2ME3Elektronika/25-26_Snack-o-Matic/Impresiones 3D/Soporte motor/Soporte Motor Completo.jpg

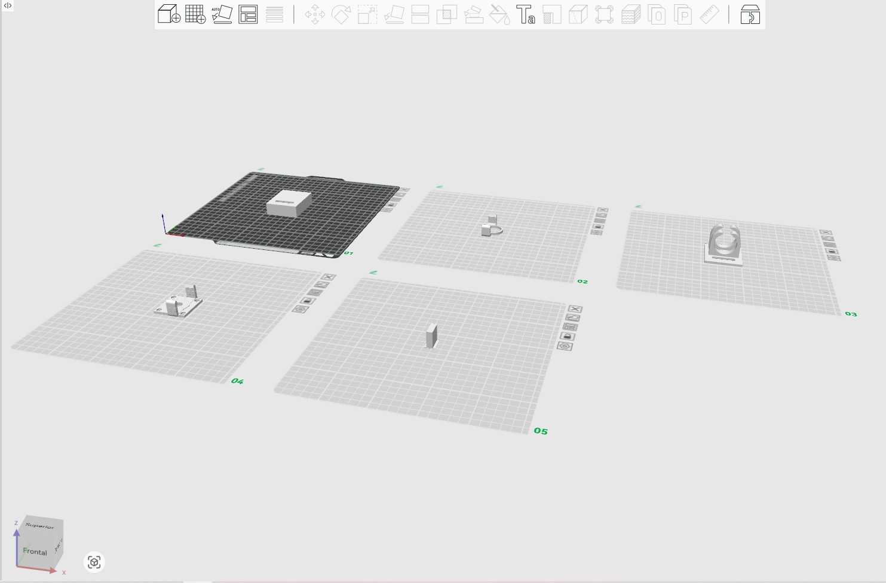
Impresiones 3D/Soporte motor/Soporte Motor Completo.jpg
