2ME3Elektronika/25-26_Snack-o-Matic/Prototipos/Prototipo foto 1.jpeg

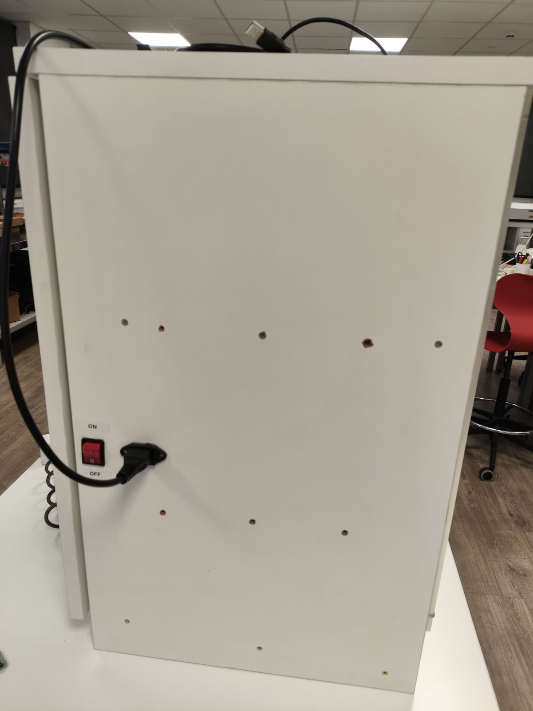
Prototipos/Prototipo foto 1.jpeg
