2ME3Elektronika/25-26_Snack-o-Matic/Impresiones 3D/Divisor de monedas/Modelos sin modificar/sorter-customizer_basebox20150919-17856-1al7uiw-0.stl

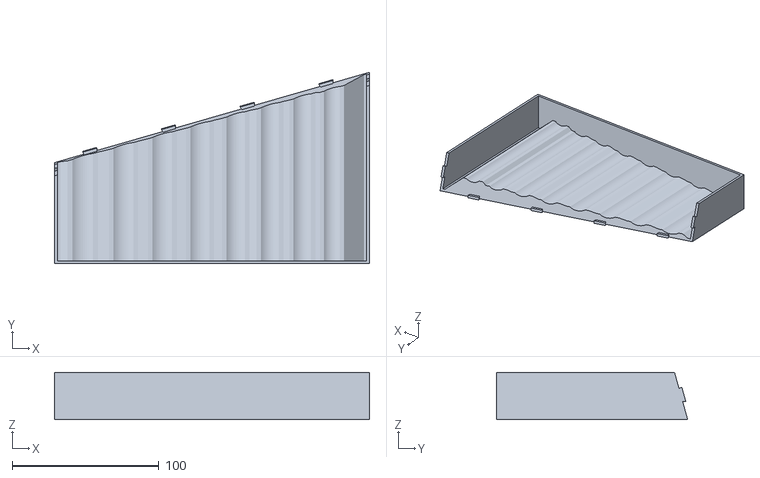
[picture p23: CAD file, 2026-01-08]
Impresiones 3D/Divisor de monedas/Modelos sin modificar/sorter-customizer_basebox20150919-17856-1al7uiw-0.stl
214.9 x 130.6 x 32.2
