2ME3Elektronika/25-26_Snack-o-Matic/Impresiones 3D/Modulos/Modulos 003.stl

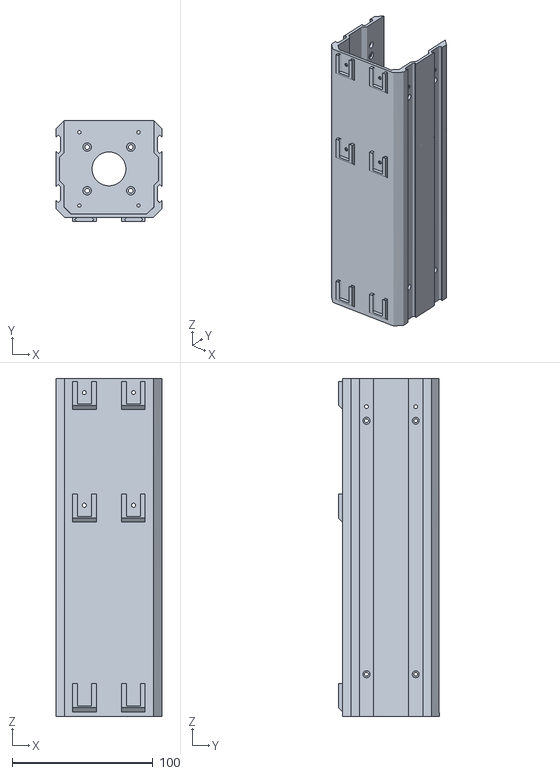
[picture p24: CAD file, 2026-06-03]
Impresiones 3D/Modulos/Modulos 003.stl
75.0 x 72.0 x 240.0
