2ME3Elektronika/25-26_Snack-o-Matic/Impresiones 3D/Monedero/Recoge monedas 4.3mf

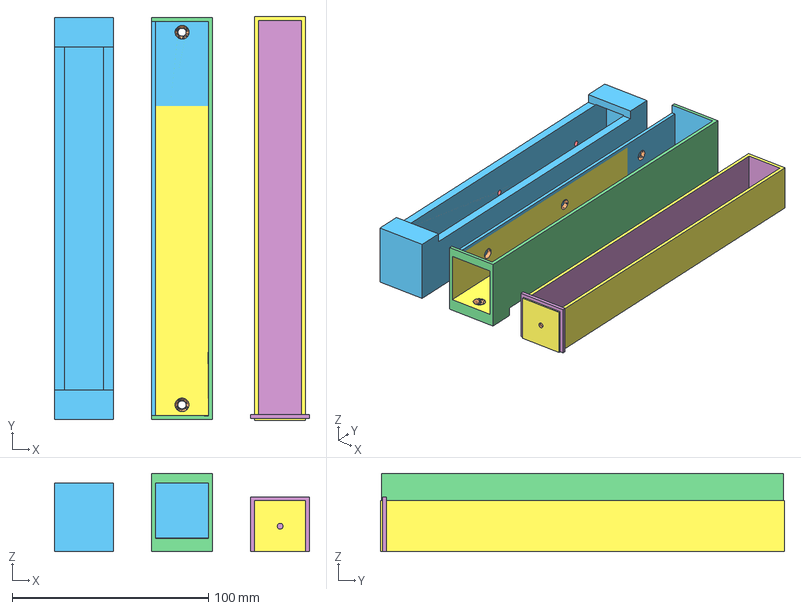
[picture p25: CAD file, 2026-06-03]
Impresiones 3D/Monedero/Recoge monedas 4.3mf
130.0 x 206.0 x 40.0 mm
