2ME3Elektronika/25-26_Snack-o-Matic/Impresiones 3D/Soporte motor/Soporte part 1.3mf

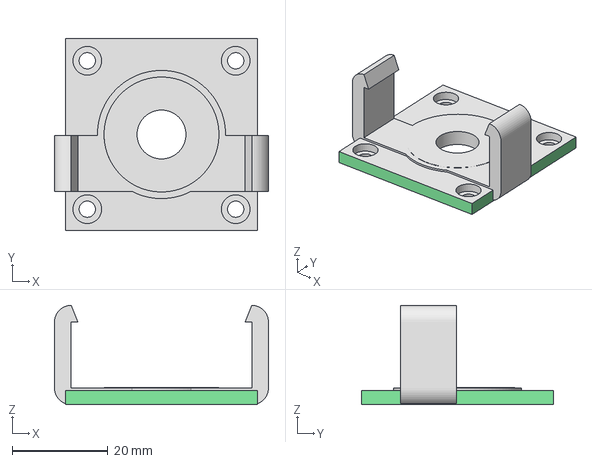
[picture p26: CAD file, 2026-06-03]
Impresiones 3D/Soporte motor/Soporte part 1.3mf
44.7 x 40.0 x 20.8 mm
