2ME3Elektronika/25-26_Snack-o-Matic/Impresiones 3D/Monedero/Cilindros_Sorter_V4.3mf

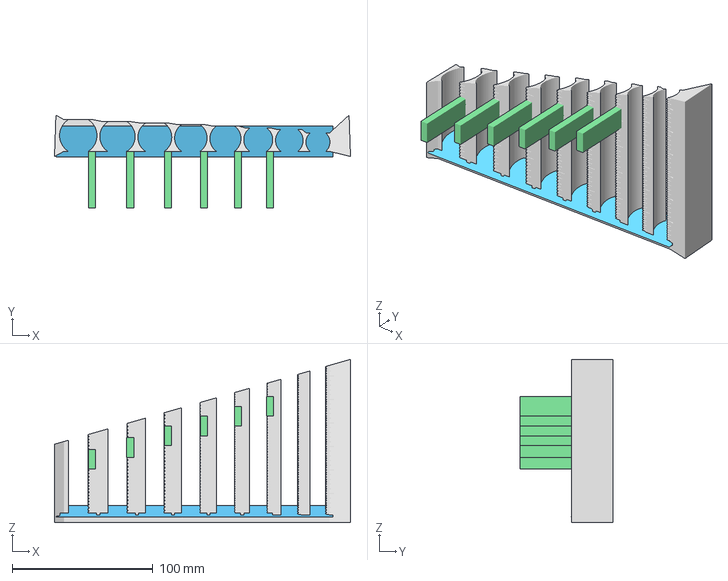
[picture p27: CAD file, 2026-06-03]
Impresiones 3D/Monedero/Cilindros_Sorter_V4.3mf
210.1 x 65.9 x 115.9 mm
