2ME3Elektronika/25-26_Snack-o-Matic/Impresiones 3D/Soporte motor/Calce  soporte motor.stl

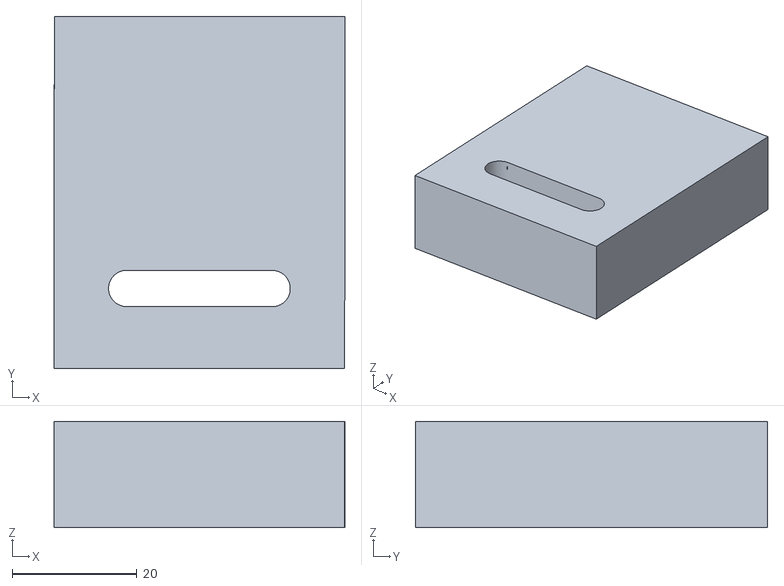
[picture p28: CAD file, 2026-06-03]
Impresiones 3D/Soporte motor/Calce soporte motor.stl
46.6 x 56.4 x 17.0
