2ME3Elektronika/25-26_Snack-o-Matic/Impresiones 3D/Devolucion 03.3mf

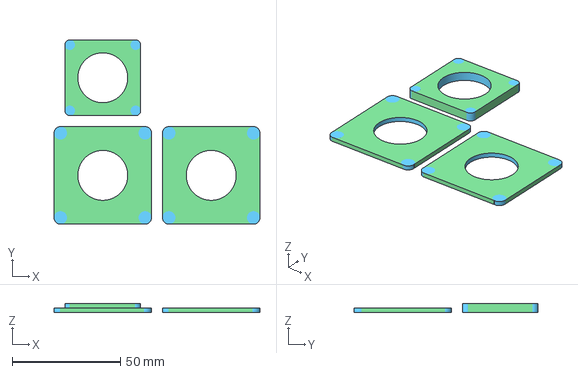
[picture p29: CAD file, 2026-06-03]
Impresiones 3D/Devolucion 03.3mf
95.0 x 85.0 x 4.00 mm
