2ME3Elektronika/25-26_Snack-o-Matic/Impresiones 3D/Divisor de monedas/Modelos personalizados/Sorter_Custom_David_V1_STL.stl

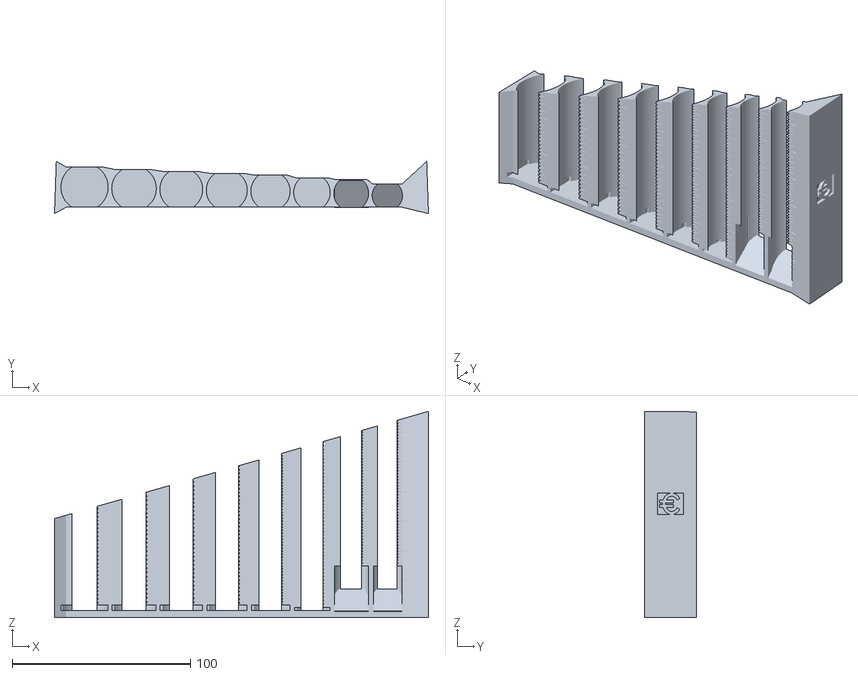
[picture p30: CAD file, 2026-01-12]
Impresiones 3D/Divisor de monedas/Modelos personalizados/Sorter_Custom_David_V1_STL.stl
210.1 x 29.4 x 115.9
