2ME3Elektronika/25-26_Snack-o-Matic/Impresiones 3D/Divisor de monedas/Modelos sin modificar/sorter-customizer_tubes20150919-17856-3ho4m5-0.stl

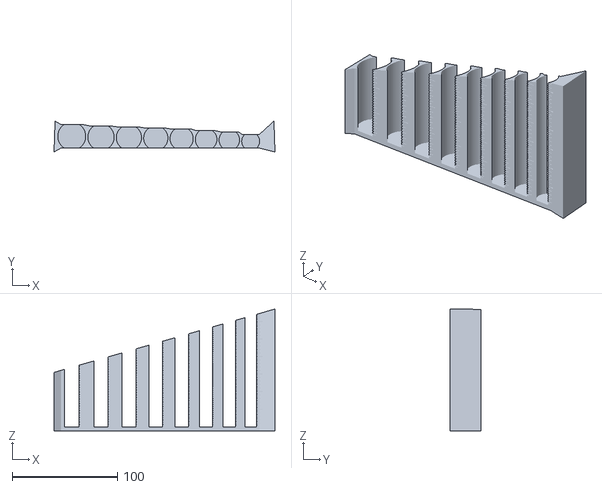
[picture p31: CAD file, 2026-01-08]
Impresiones 3D/Divisor de monedas/Modelos sin modificar/sorter-customizer_tubes20150919-17856-3ho4m5-0.stl
210.1 x 29.4 x 115.9
