2ME3Elektronika/25-26_Snack-o-Matic/Impresiones 3D/Monedero/M3.stl

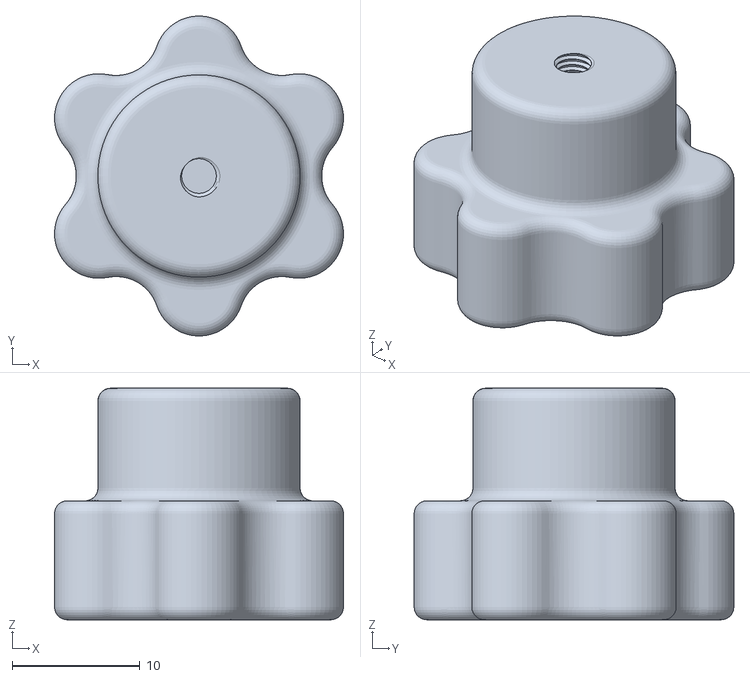
[picture p32: CAD file, 2026-06-03]
Impresiones 3D/Monedero/M3.stl
22.6 x 25.0 x 18.1
