2ME3Elektronika/25-26_Snack-o-Matic/Impresiones 3D/Soporte motor/Soporte Motor completo.3mf

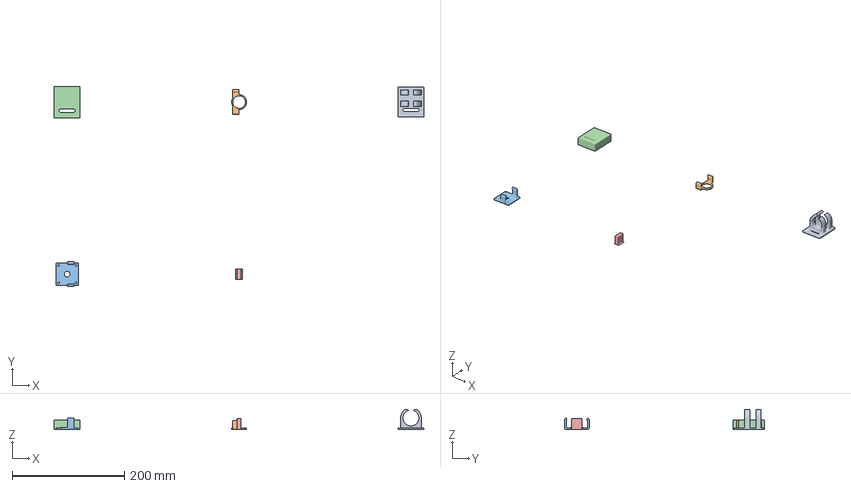
[picture p33: CAD file, 2026-06-03]
Impresiones 3D/Soporte motor/Soporte Motor completo.3mf
660.6 x 357.7 x 36.5 mm
MotorBracket006.stl
MotorBracket Part 3.stl
calce Motor.stl
cierre.stl
