2ME3Elektronika/25-26_Snack-o-Matic/Impresiones 3D/Monedero/Separador altura 20mm.stl

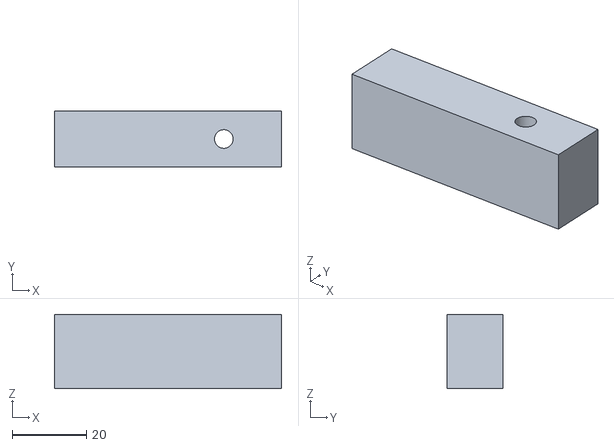
[picture p34: CAD file, 2026-06-03]
Impresiones 3D/Monedero/Separador altura 20mm.stl
61.0 x 15.0 x 20.0
