2ME3Elektronika/25-26_Snack-o-Matic/Impresiones 3D/tapa para circuito v7.3mf

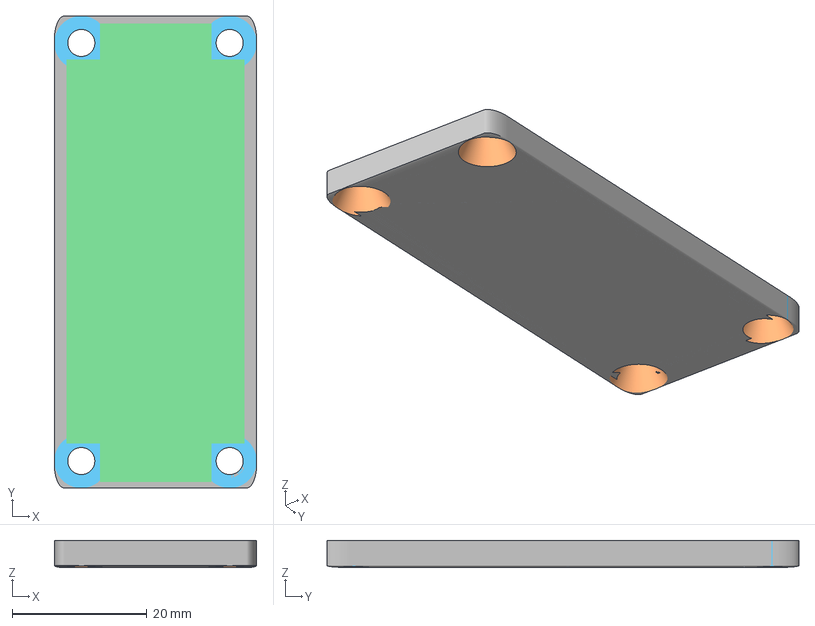
[picture p35: CAD file, 2026-06-03]
Impresiones 3D/tapa para circuito v7.3mf
30.0 x 70.0 x 4.03 mm
