2ME3Elektronika/25-26_Snack-o-Matic/Impresiones 3D/Monedero/Recoge monedas central.stl

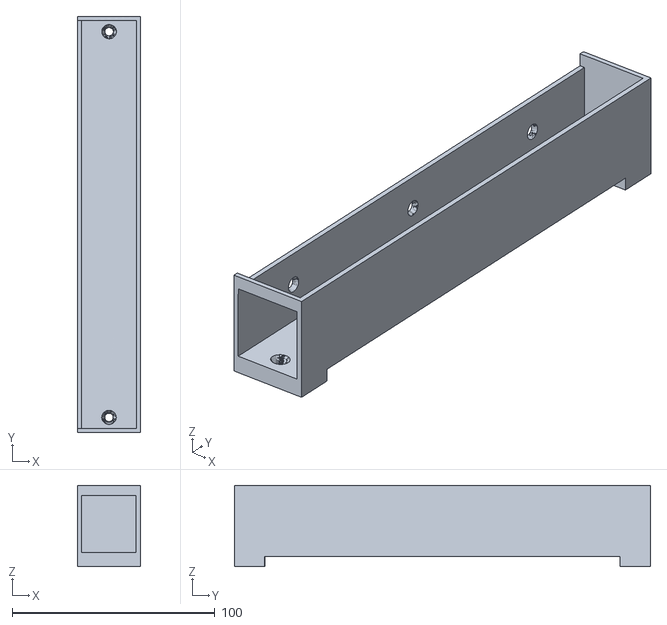
[picture p36: CAD file, 2026-06-03]
Impresiones 3D/Monedero/Recoge monedas central.stl
31.0 x 204.9 x 40.0
