2ME3Elektronika/25-26_Snack-o-Matic/Impresiones 3D/panel lateral V2.3mf

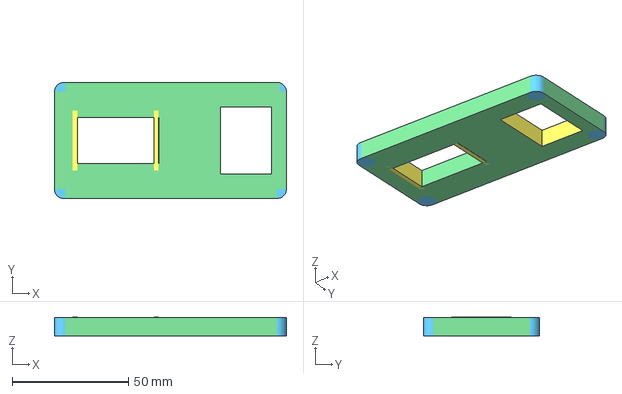
[picture p37: CAD file, 2026-06-03]
Impresiones 3D/panel lateral V2.3mf
100.0 x 50.0 x 8.00 mm
