2ME3Elektronika/25-26_Snack-o-Matic/Impresiones 3D/Monedero/Guia v2.stl

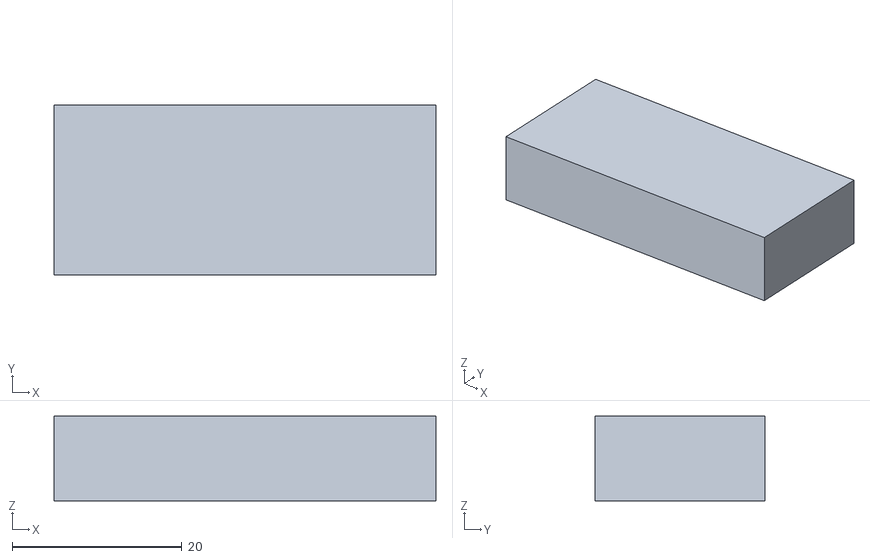
[picture p38: CAD file, 2026-06-03]
Impresiones 3D/Monedero/Guia v2.stl
45.0 x 20.0 x 10.0
