2ME3Elektronika/25-26_Snack-o-Matic/Impresiones 3D/Monedero/Separador lateral v2.stl

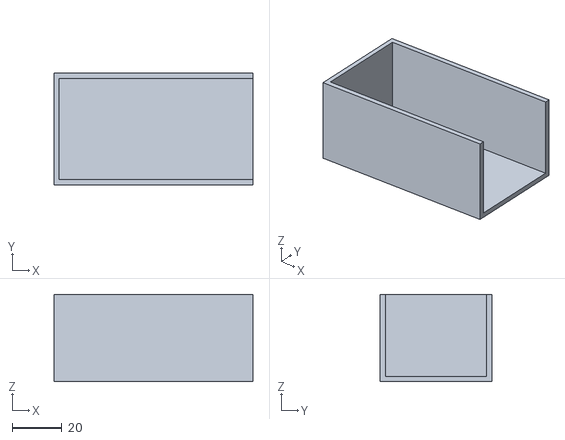
[picture p39: CAD file, 2026-06-03]
Impresiones 3D/Monedero/Separador lateral v2.stl
80.0 x 45.0 x 35.0
