2ME3Elektronika/25-26_Snack-o-Matic/Impresiones 3D/Monedero/traga monedas v8.stl

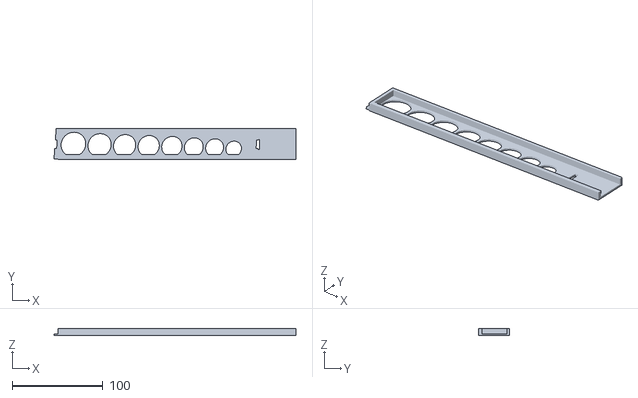
[picture p40: CAD file, 2026-06-03]
Impresiones 3D/Monedero/traga monedas v8.stl
266.5 x 34.6 x 8.00
