2ME3Elektronika/25-26_Snack-o-Matic/Impresiones 3D/Monedero/Travesaño.stl

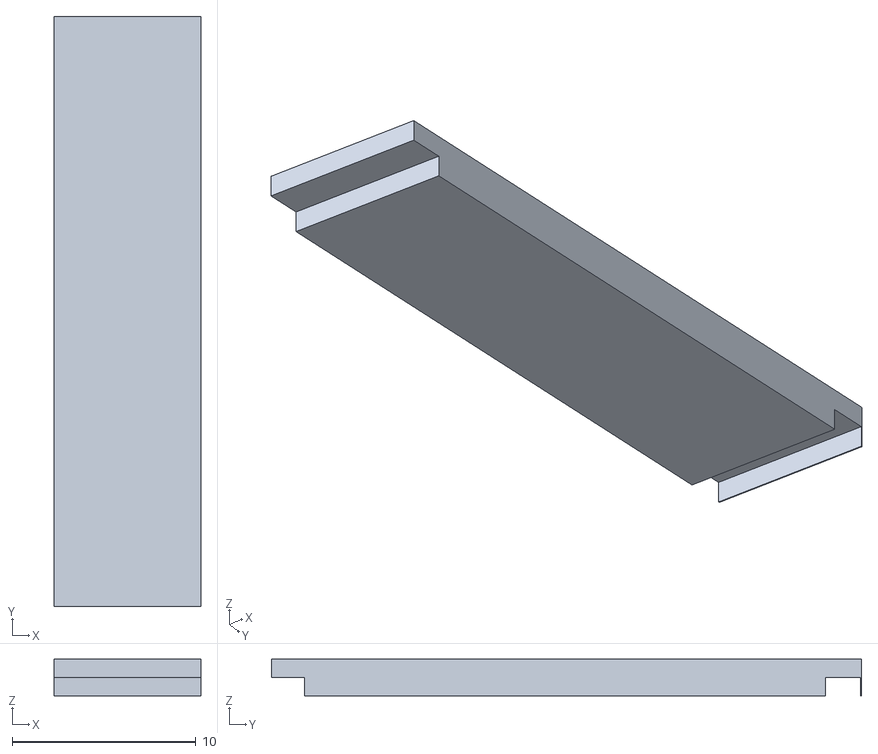
[picture p41: CAD file, 2026-06-03]
Impresiones 3D/Monedero/Travesaño.stl
8.00 x 32.2 x 2.00
