2ME3Elektronika/25-26_Snack-o-Matic/Impresiones 3D/Monedero/Chasis_Sorter_V2.3mf

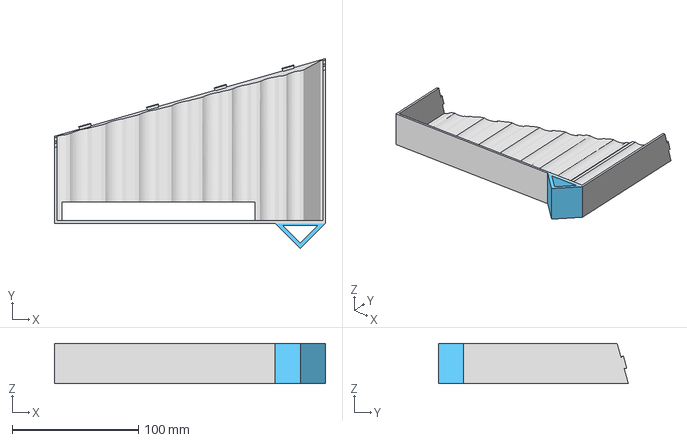
[picture p42: CAD file, 2026-05-22]
Impresiones 3D/Monedero/Chasis_Sorter_V2.3mf
214.9 x 150.6 x 32.1 mm
